kvnyng/Orpheus-Leap-Micro/Case/PCB 3D Model - detailed/Renderings/Orpheus_Leap_Micro_2021-Mar-10_06-57-49AM-000_CustomizedView12856644847_png.png

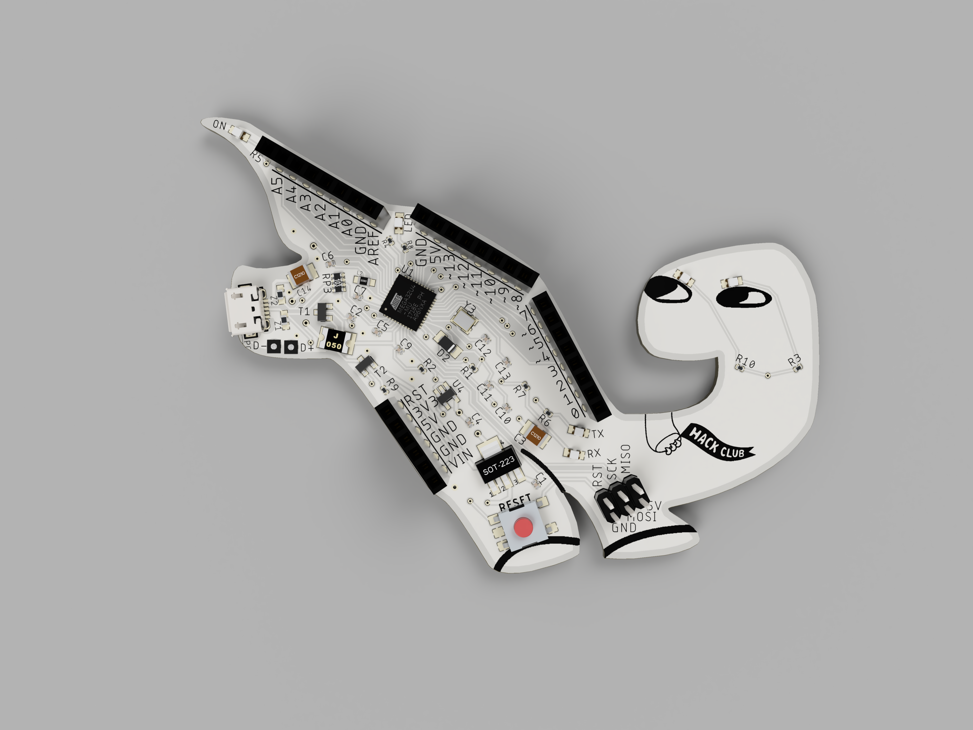
Case/PCB 3D Model - detailed/Renderings/Orpheus_Leap_Micro_2021-Mar-10_06-57-49AM-000_CustomizedView12856644847_png.png
