kvnyng/Orpheus-Leap-Micro/Case/PCB 3D Model - detailed/Renderings/Orpheus_Leap_Micro_2021-Mar-10_08-26-49AM-000_CustomizedView17127822511_png.png

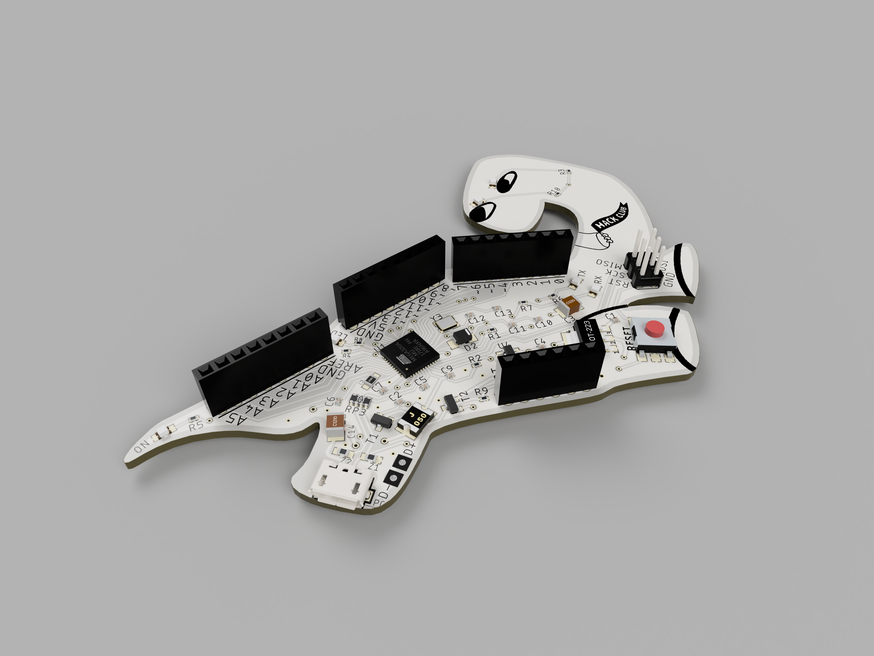
Case/PCB 3D Model - detailed/Renderings/Orpheus_Leap_Micro_2021-Mar-10_08-26-49AM-000_CustomizedView17127822511_png.png
