kvnyng/Orpheus-Leap-Micro/Case/PCB 3D Model - detailed/Renderings/Orpheus_Leap_Micro_2021-Mar-10_10-49-29AM-000_CustomizedView25779600010_png.png

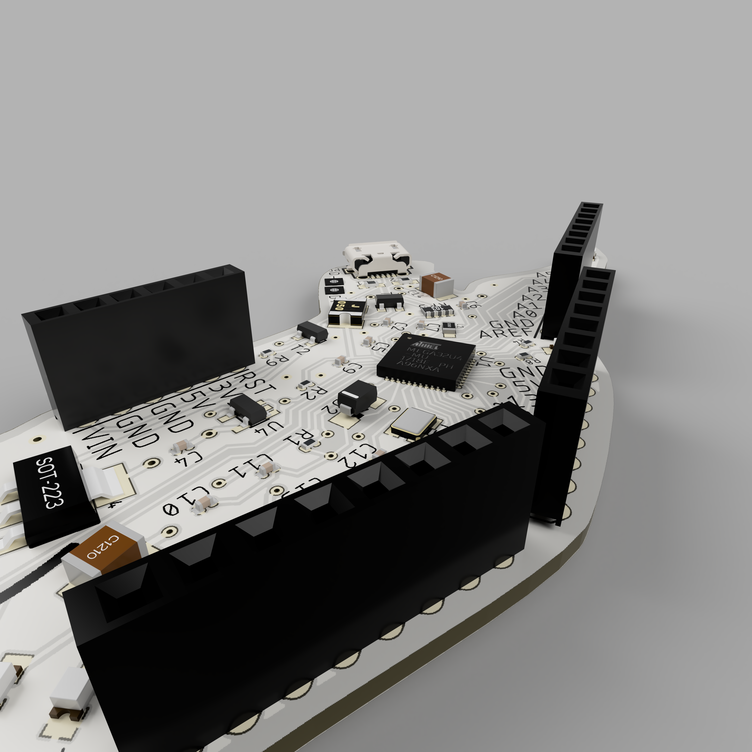
Case/PCB 3D Model - detailed/Renderings/Orpheus_Leap_Micro_2021-Mar-10_10-49-29AM-000_CustomizedView25779600010_png.png
