kvnyng/Orpheus-Leap-Micro/Case/PCB 3D Model - detailed/Renderings/Orpheus_Leap_Micro_2021-Mar-10_10-50-15AM-000_CustomizedView39839070488_png.png

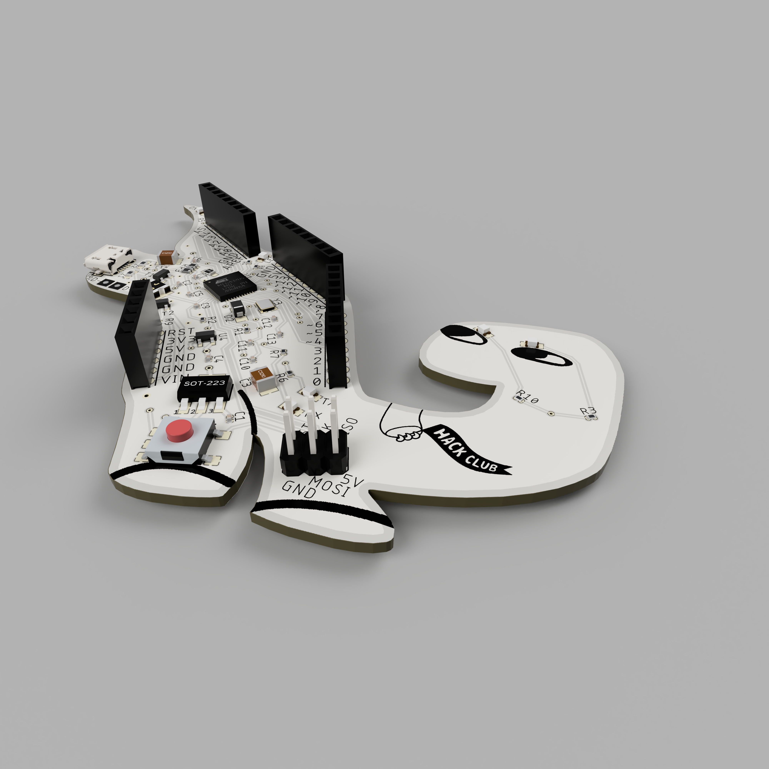
Case/PCB 3D Model - detailed/Renderings/Orpheus_Leap_Micro_2021-Mar-10_10-50-15AM-000_CustomizedView39839070488_png.png
